andyw-lala/Tek7KTesters/Images/Aux_Y.png

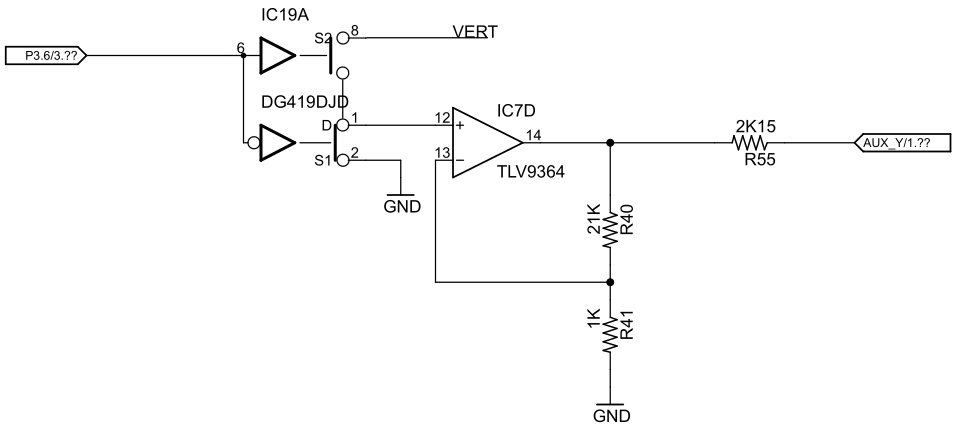
Images/Aux_Y.png
