andyw-lala/Tek7KTesters/Images/Aux_Z_Generator_20250103.png

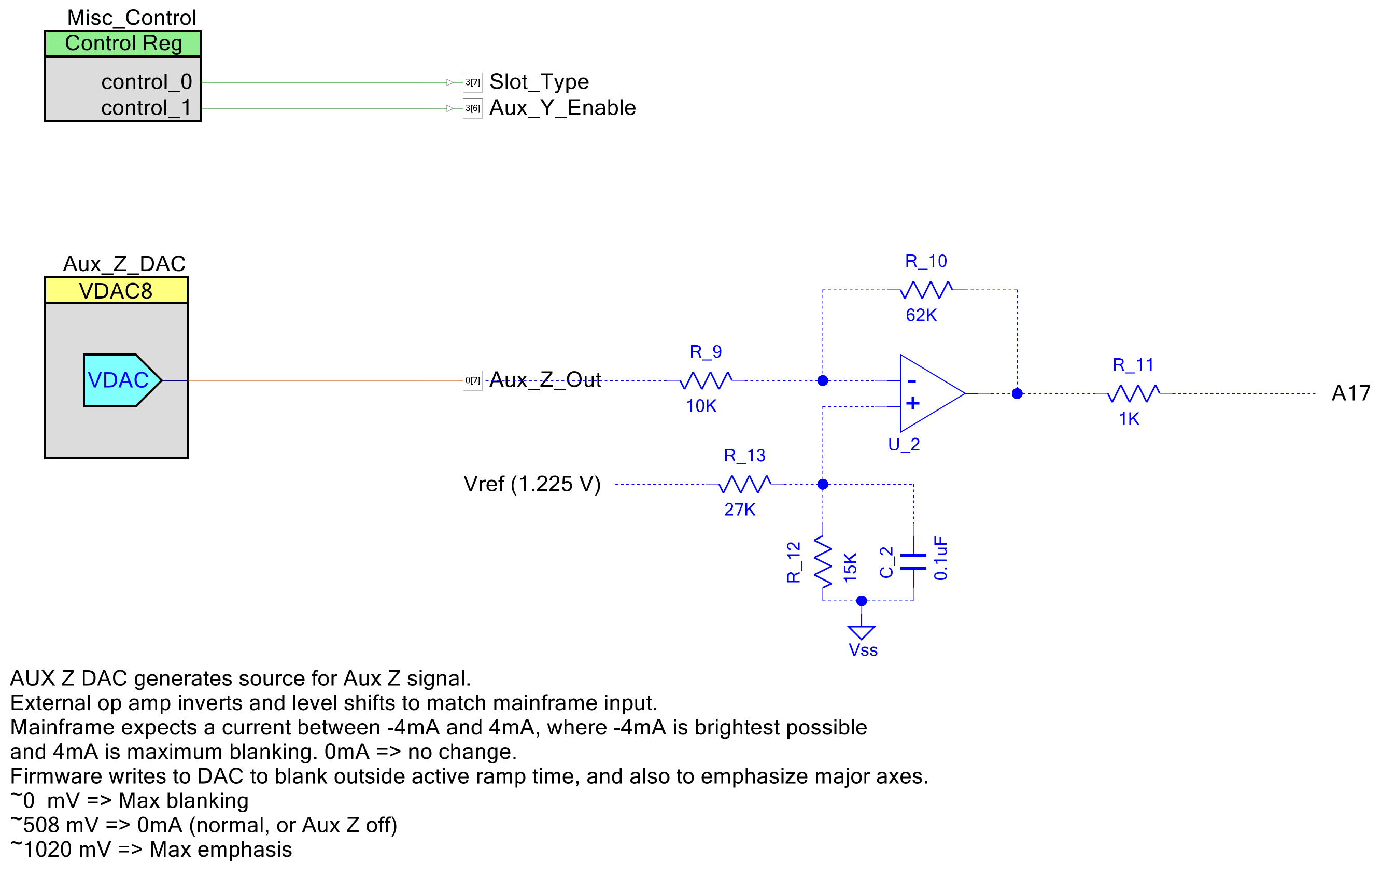
Images/Aux_Z_Generator_20250103.png
