andyw-lala/Tek7KTesters/Images/Discrete_timeslot_interface_snippet.png

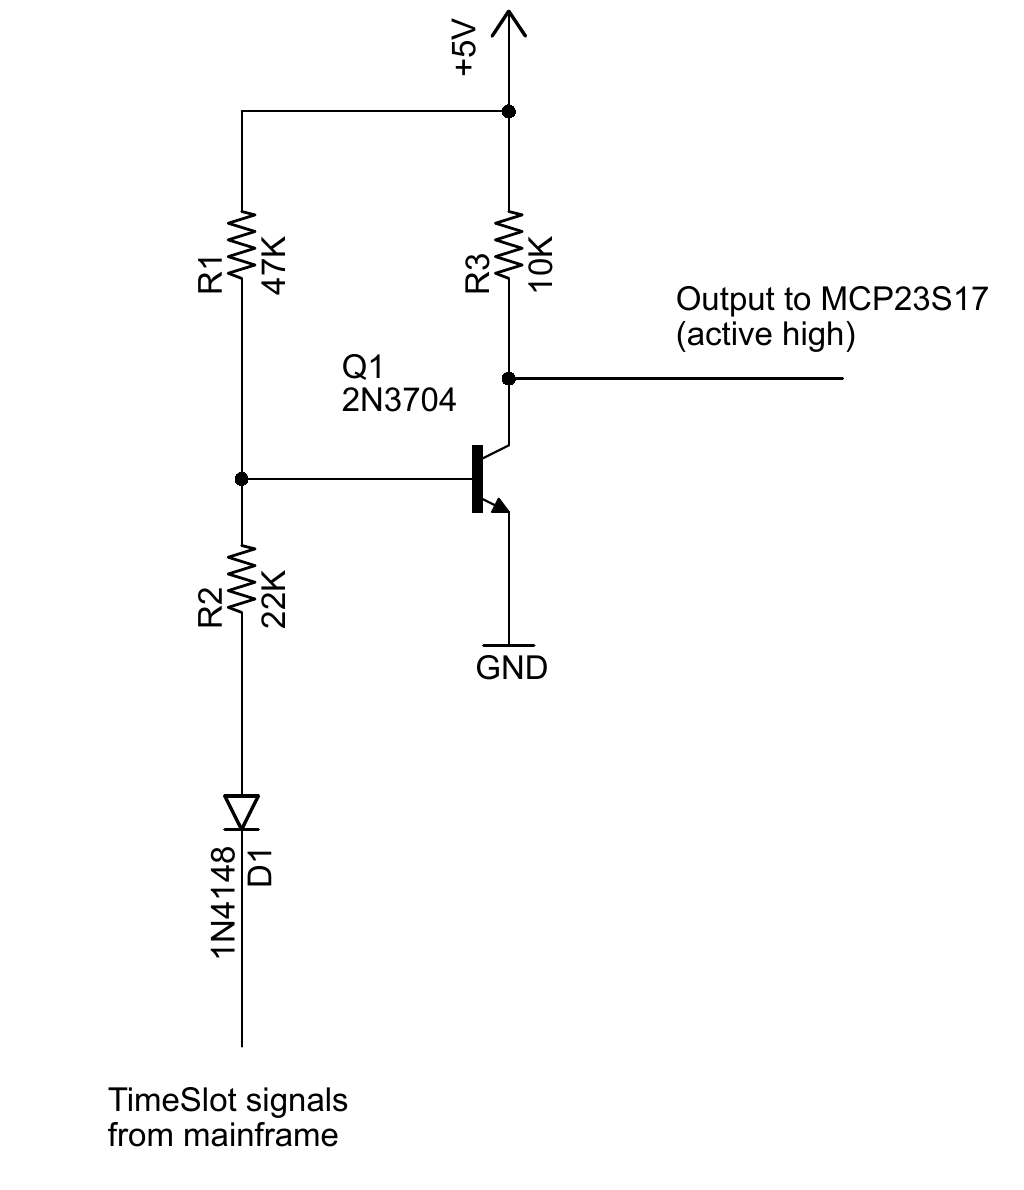
Images/Discrete_timeslot_interface_snippet.png
