andyw-lala/Tek7KTesters/Images/Ramp_Generator_20250103.png

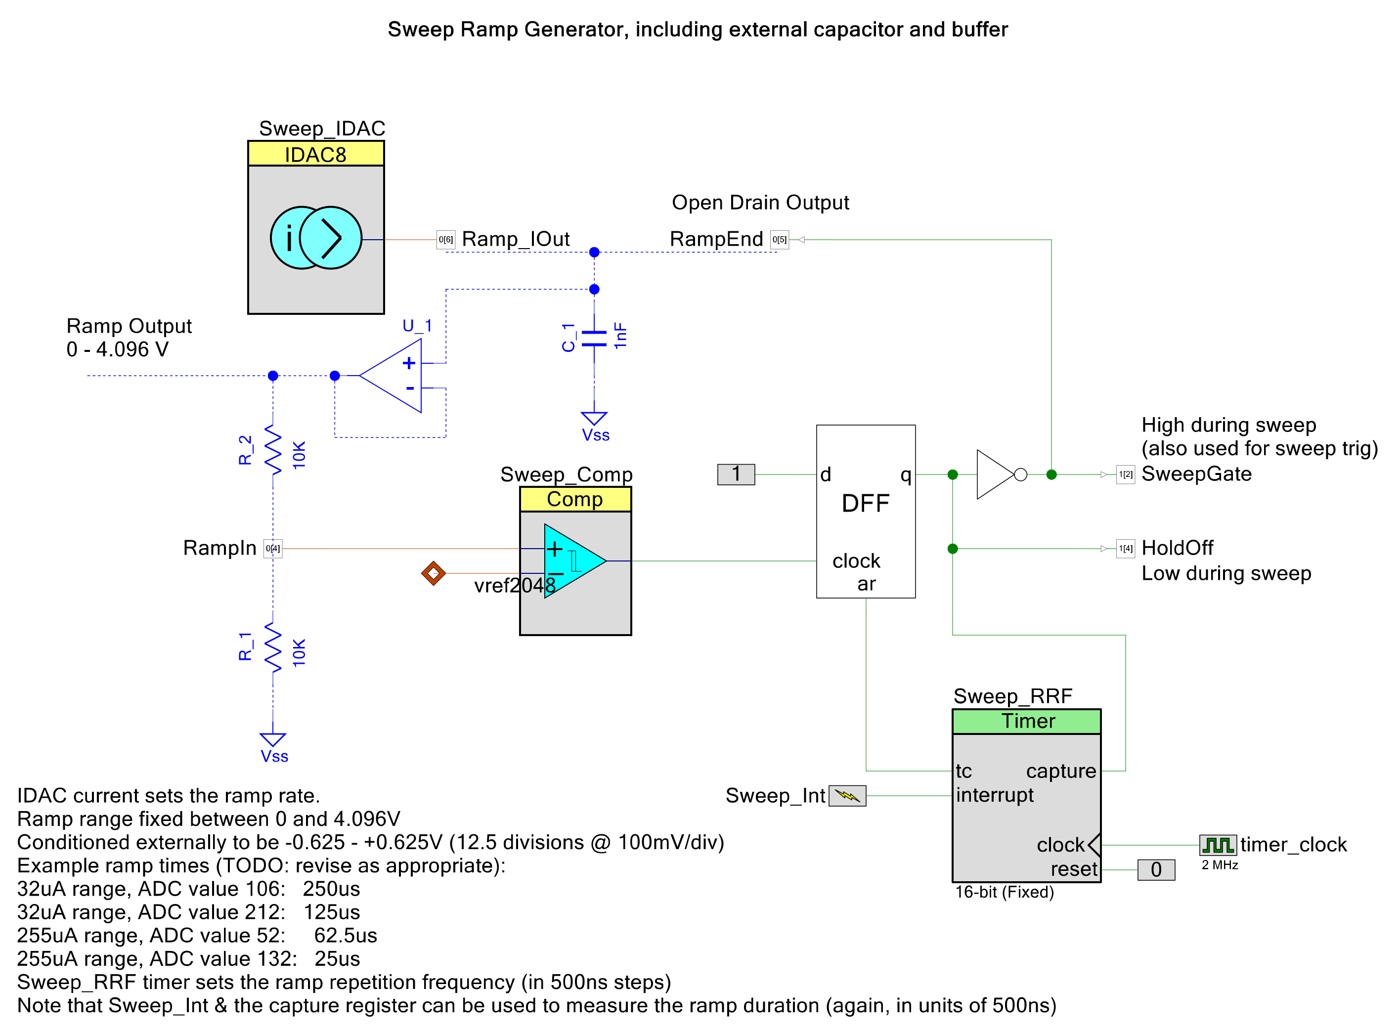
Images/Ramp_Generator_20250103.png
