andyw-lala/Tek7KTesters/Images/Readout_current_all.png

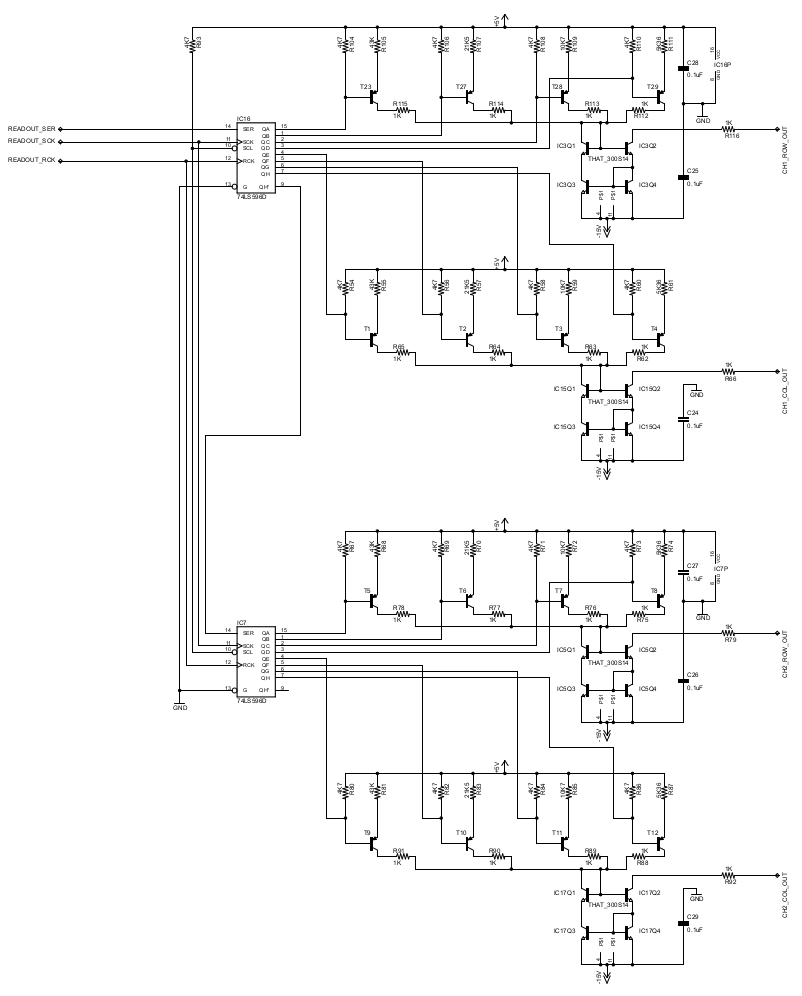
Images/Readout_current_all.png
