andyw-lala/Tek7KTesters/Images/Schmitt_trigger_timeslot_interface_snippet.png

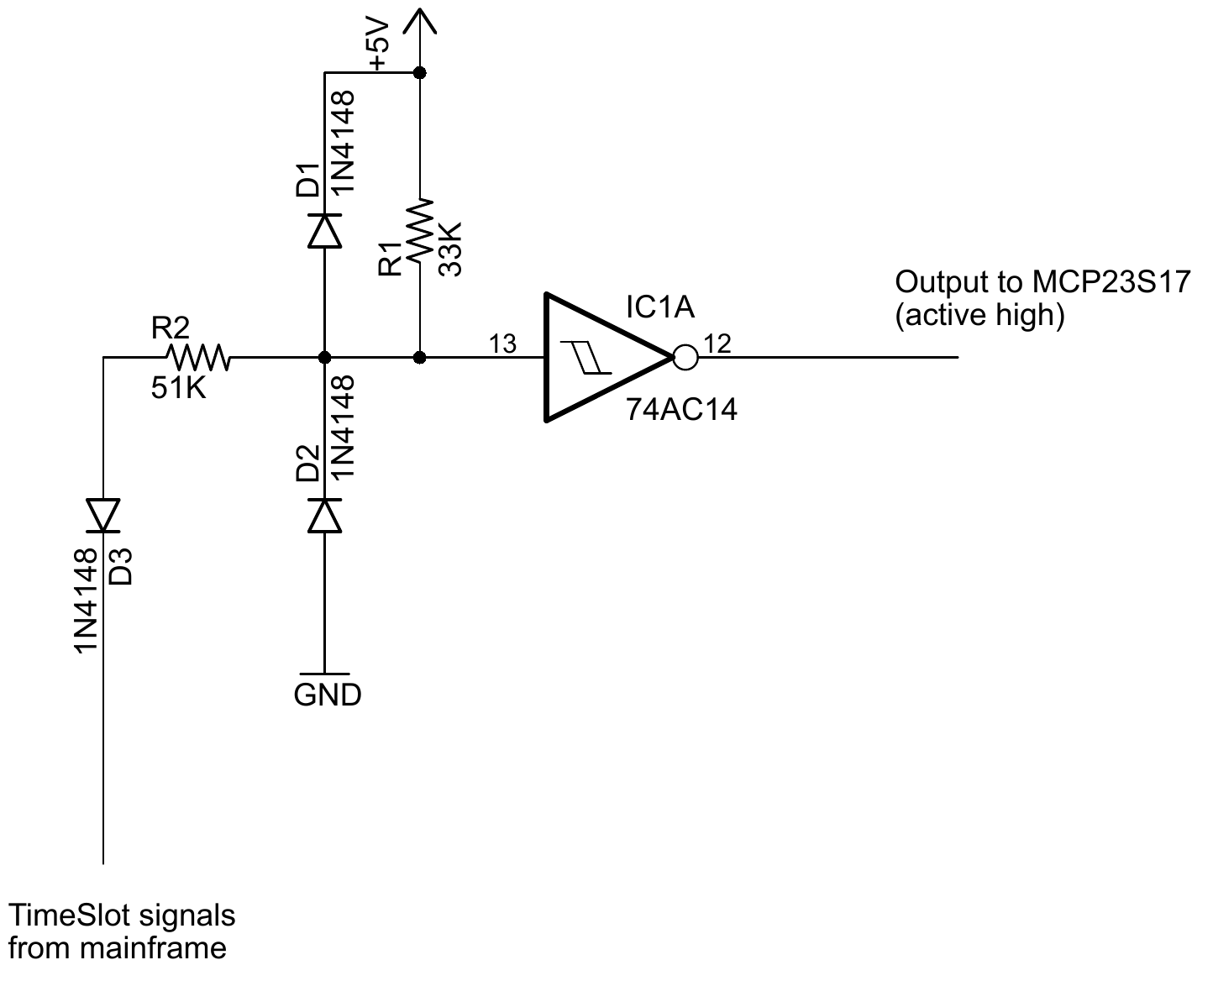
Images/Schmitt_trigger_timeslot_interface_snippet.png
