andyw-lala/Tek7KTesters/Images/Tek7K-TS0-202107271813.png

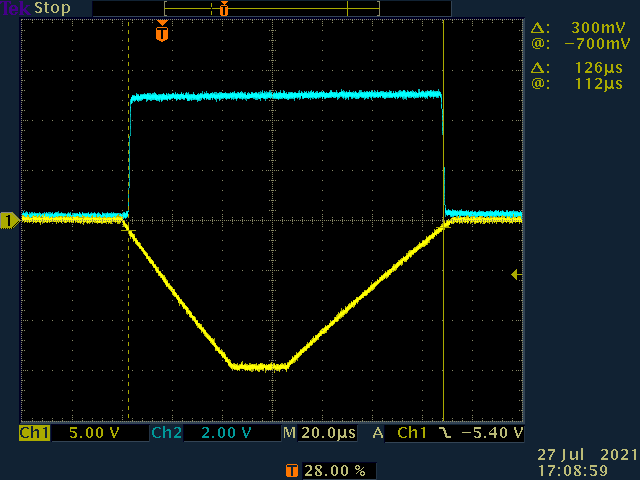
Images/Tek7K-TS0-202107271813.png
