andyw-lala/Tek7KTesters/Images/Tek7K-TS0-202107281441.png

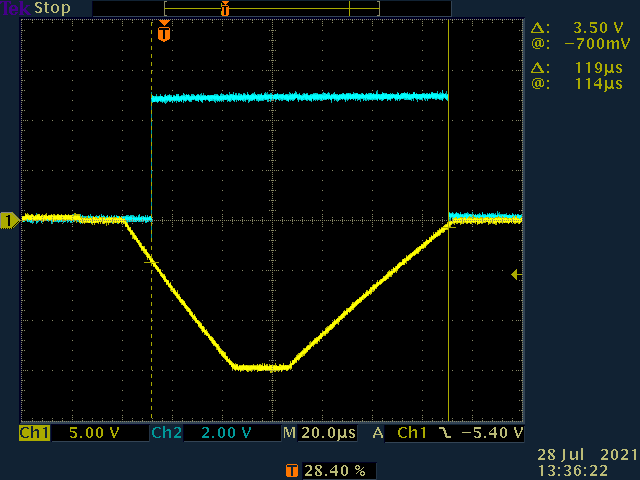
Images/Tek7K-TS0-202107281441.png
