andyw-lala/Tek7KTesters/Images/TS_Current_Sink.png

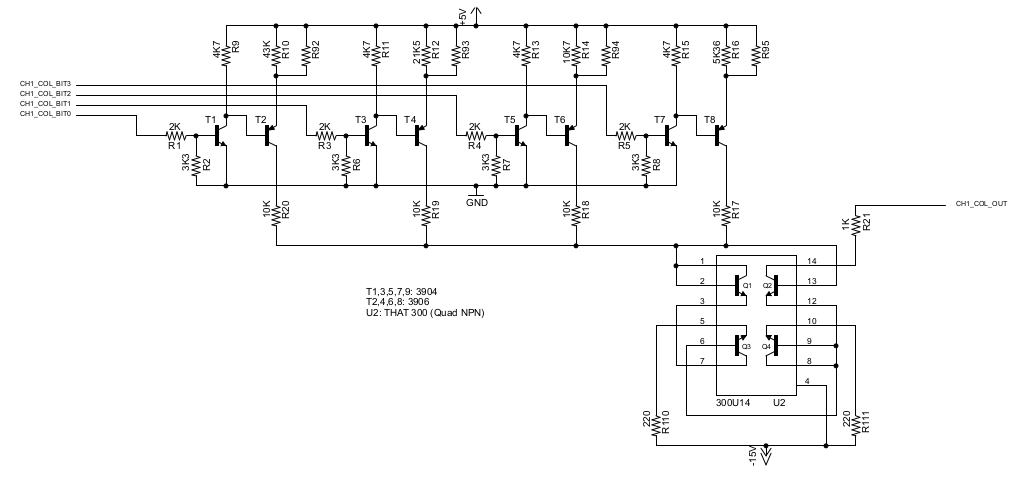
Images/TS_Current_Sink.png
