andyw-lala/Tek7KTesters/Images/TS_Current_Sink_2.png

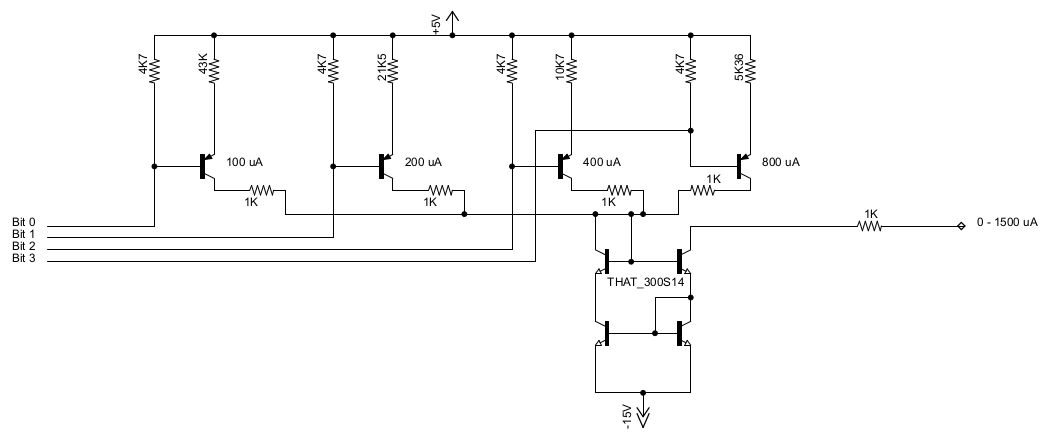
Images/TS_Current_Sink_2.png
