andyw-lala/Tek7KTesters/Images/TS_Output_Logic.png

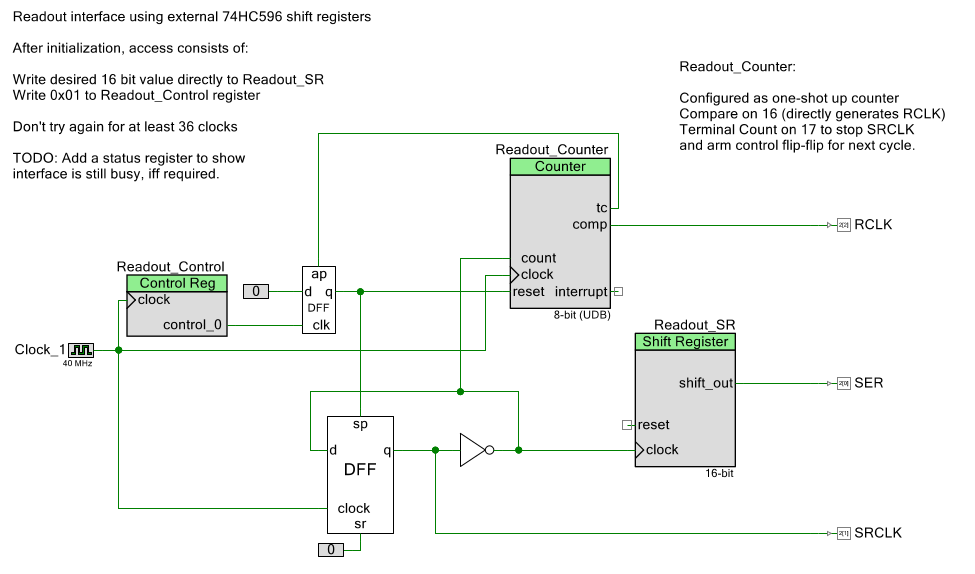
Images/TS_Output_Logic.png
