andyw-lala/Tek7KTesters/Images/TS_Pulse_Input_ISR_Timing.png

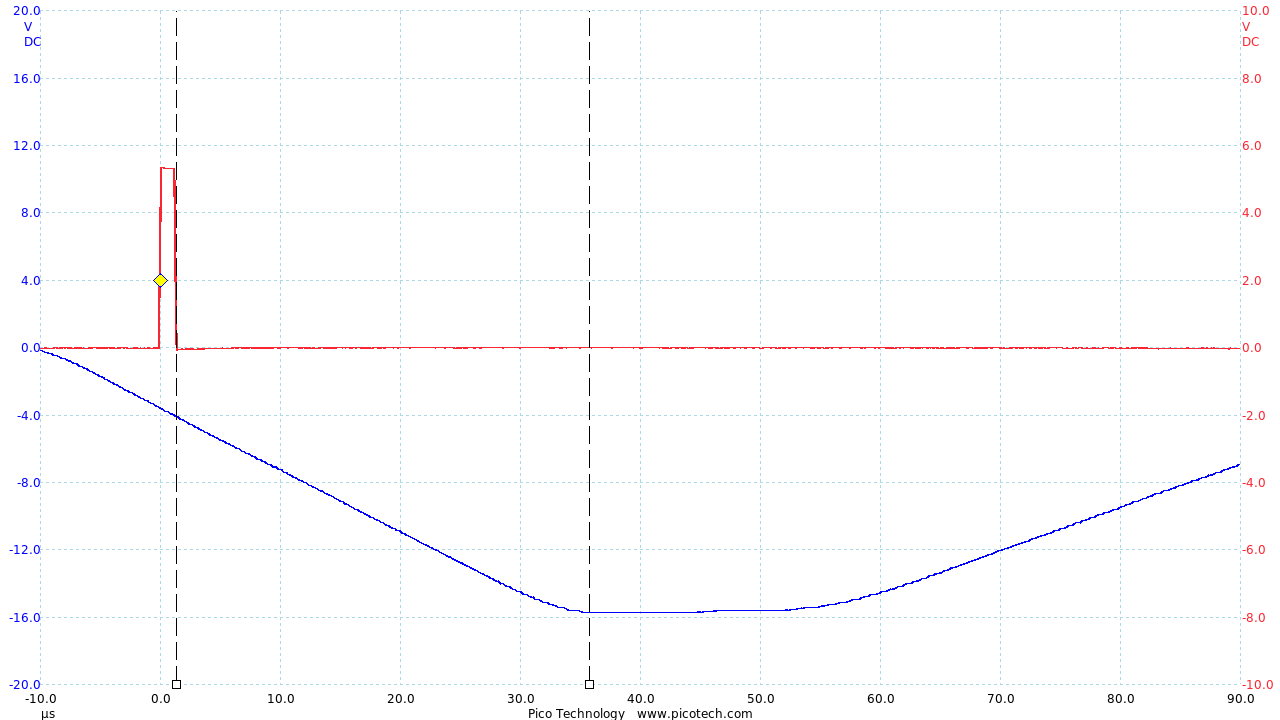
Images/TS_Pulse_Input_ISR_Timing.png
