andyw-lala/Tek7KTesters/Images/TS_Pulse_Inputs.png

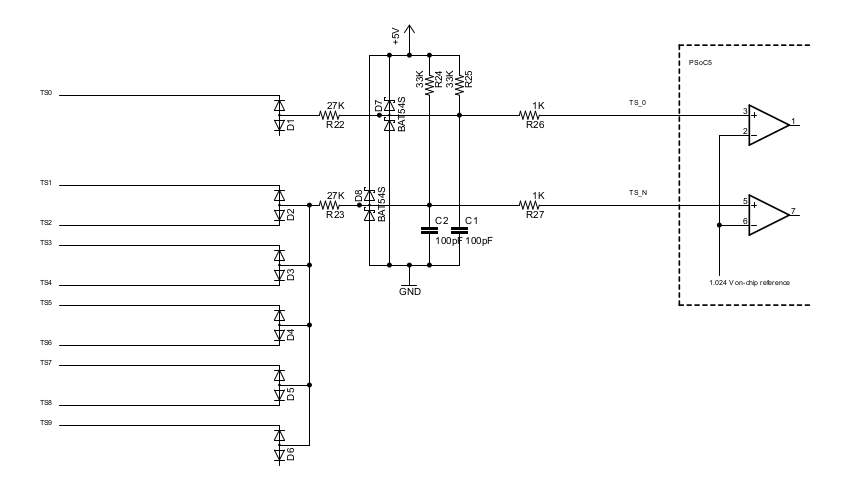
Images/TS_Pulse_Inputs.png
