andyw-lala/Tek7KTesters/Images/Step_Generators_20250103.png

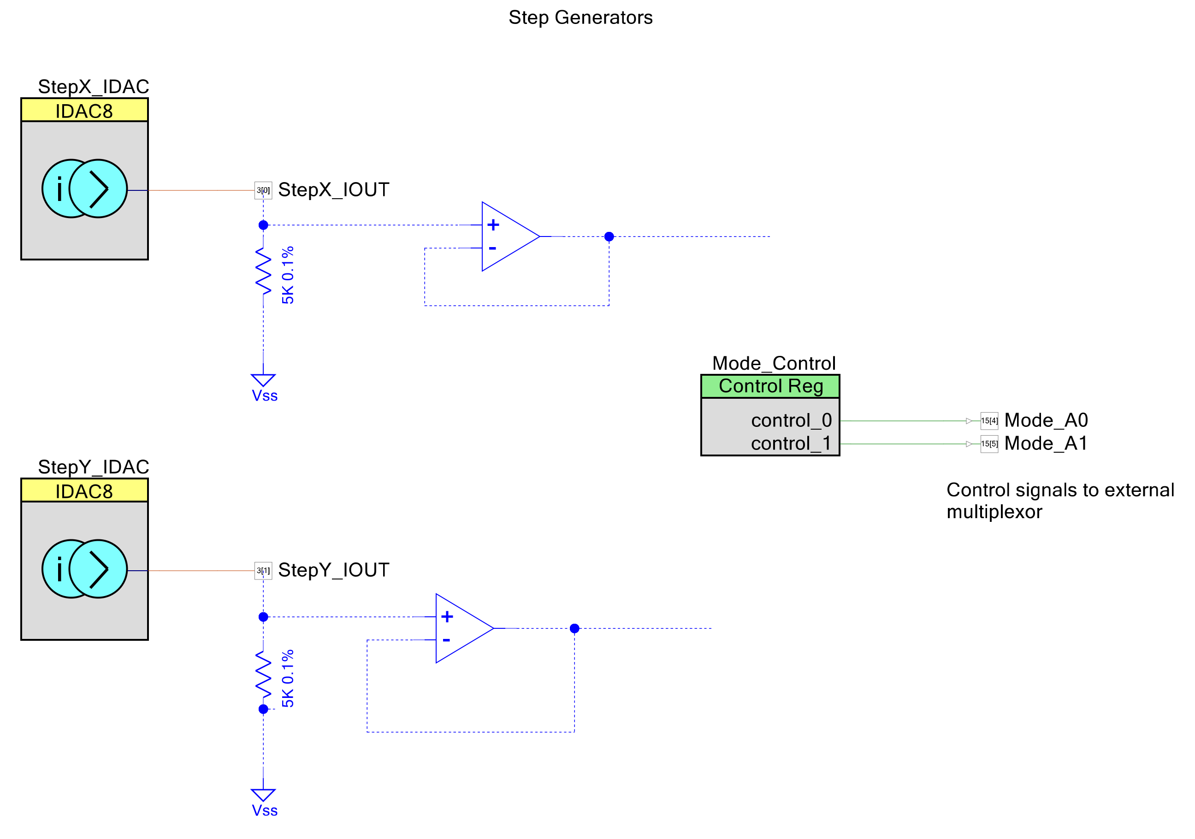
Images/Step_Generators_20250103.png
