andyw-lala/Tek7KTesters/Images/Steps.png

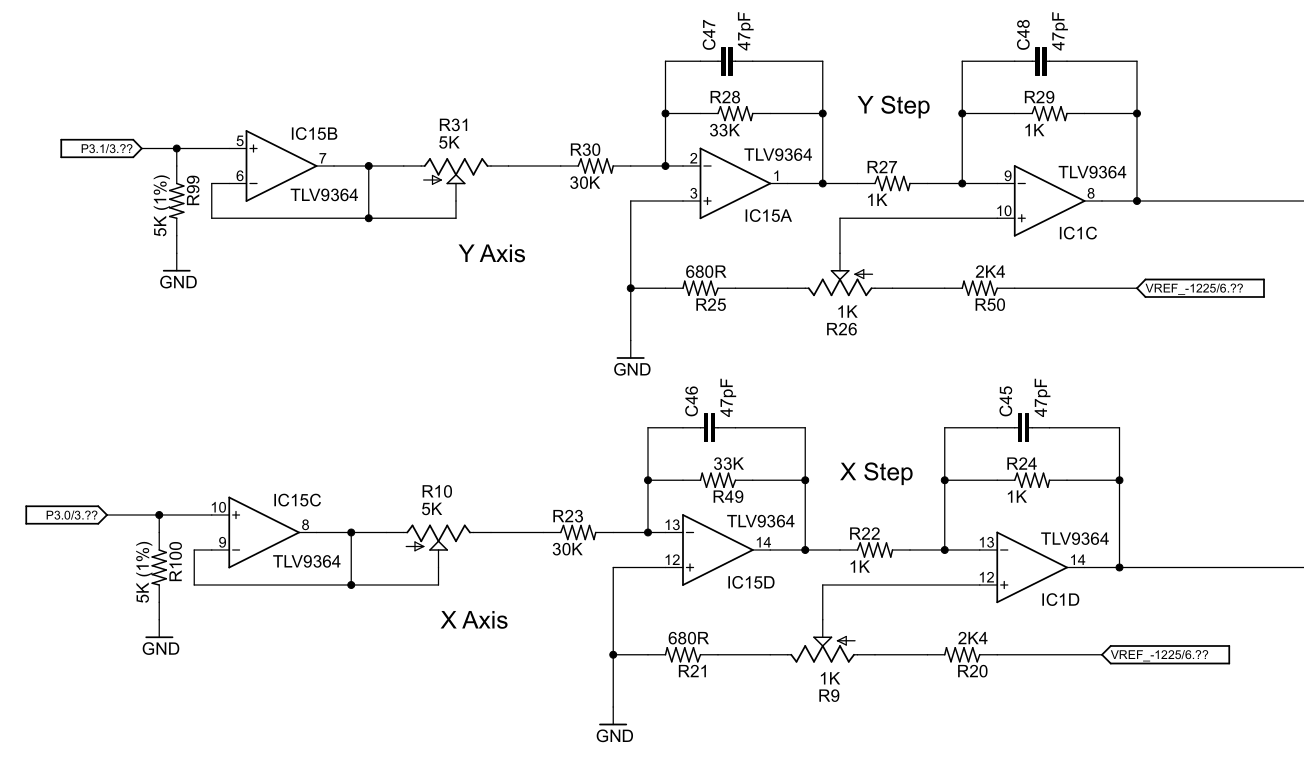
Images/Steps.png
