andyw-lala/Tek7KTesters/Tek7KTester_PSOC/Prototype_01.cydsn/lcd.c

#include "project.h"
#include "lcd.h"


	   
_lcd_dev lcddev;

uint16 POINT_COLOR = 0x0000,BACK_COLOR = 0xFFFF;  
uint16 DeviceCode;	 

/*****************************************************************************
 * @name       :void LCD_WR_REG(uint8 data)
 * @date       :2018-08-09 
 * @function   :Write an 8-bit command to the LCD screen
 * @parameters :data:Command value to be written
 * @retvalue   :None
******************************************************************************/
void LCD_WR_REG(uint8 data)
{ 
    LCD_CS_CLR;     
    LCD_RS_CLR;	  
    Display_SPI_WriteByte(data);
    LCD_CS_SET;	
}

/*****************************************************************************
 * @name       :void LCD_WR_DATA(uint8 data)
 * @date       :2018-08-09 
 * @function   :Write an 8-bit data to the LCD screen
 * @parameters :data:data value to be written
 * @retvalue   :None
******************************************************************************/
void LCD_WR_DATA(uint8 data)
{
    LCD_CS_CLR;
    LCD_RS_SET;
    Display_SPI_WriteByte(data);
    LCD_CS_SET;
}

/*****************************************************************************
 * @name       :void LCD_WriteReg(uint8 LCD_Reg, uint16 LCD_RegValue)
 * @date       :2018-08-09 
 * @function   :Write data into registers
 * @parameters :LCD_Reg:Register address
                LCD_RegValue:Data to be written
 * @retvalue   :None
******************************************************************************/
void LCD_WriteReg(uint8 LCD_Reg, uint16 LCD_RegValue)
{	
    LCD_WR_REG(LCD_Reg);  
    LCD_WR_DATA(LCD_RegValue);	    		 
}	   

/*****************************************************************************
 * @name       :void LCD_WriteRAM_Prepare(void)
 * @date       :2018-08-09 
 * @function   :Write GRAM
 * @parameters :None
 * @retvalue   :None
******************************************************************************/	 
void LCD_WriteRAM_Prepare(void)
{
    LCD_WR_REG(lcddev.wramcmd);
}	 

/*****************************************************************************
 * @name       :void Lcd_WriteData_16Bit(uint16 Data)
 * @date       :2018-08-09 
 * @function   :Write an 16-bit command to the LCD screen
 * @parameters :Data:Data to be written
 * @retvalue   :None
******************************************************************************/	 
void Lcd_WriteData_16Bit(uint16 Data)
{	
    LCD_CS_CLR;
    LCD_RS_SET;  
    Display_SPI_WriteByte(Data>>8);
    Display_SPI_WriteByte(Data);
    LCD_CS_SET;
}

/*****************************************************************************
 * @name       :void LCD_DrawPoint(uint16 x,uint16 y)
 * @date       :2018-08-09 
 * @function   :Write a pixel data at a specified location
 * @parameters :x:the x coordinate of the pixel
                y:the y coordinate of the pixel
 * @retvalue   :None
******************************************************************************/	
void LCD_DrawPoint(uint16 x,uint16 y)
{
    LCD_SetCursor(x,y);
    Lcd_WriteData_16Bit(POINT_COLOR); 
}

/*****************************************************************************
 * @name       :void LCD_Clear(uint16 Color)
 * @date       :2018-08-09 
 * @function   :Full screen filled LCD screen
 * @parameters :color:Filled color
 * @retvalue   :None
******************************************************************************/	
void LCD_Clear(uint16 Color)
{
    unsigned int i,m;  
    LCD_SetWindows(0,0,lcddev.width-1,lcddev.height-1);   
    LCD_CS_CLR;
    LCD_RS_SET;
    for(i=0;i<lcddev.height;i++) {
        for(m=0;m<lcddev.width;m++) {	
            Lcd_WriteData_16Bit(Color);
        }
    }
    LCD_CS_SET;
} 

/*****************************************************************************
 * @name       :void LCD_RESET(void)
 * @date       :2018-08-09 
 * @function   :Reset LCD screen
 * @parameters :None
 * @retvalue   :None
******************************************************************************/	
void LCD_RESET(void)
{
    LCD_RST_CLR;
    CyDelay(100);	
    LCD_RST_SET;
    CyDelay(50);
}

/*****************************************************************************
 * @name       :void LCD_RESET(void)
 * @date       :2018-08-09 
 * @function   :Initialization LCD screen
 * @parameters :None
 * @retvalue   :None
******************************************************************************/	 	 
void LCD_Init(void)
{  
    Display_SPI_Start();
    
    LCD_RESET();
    
    LCD_WR_REG(0xCF);  
    LCD_WR_DATA(0x00); 
    LCD_WR_DATA(0xD9); //0xC1 
    LCD_WR_DATA(0X30); 
    LCD_WR_REG(0xED);  
    LCD_WR_DATA(0x64); 
    LCD_WR_DATA(0x03); 
    LCD_WR_DATA(0X12); 
    LCD_WR_DATA(0X81); 
    LCD_WR_REG(0xE8);  
    LCD_WR_DATA(0x85); 
    LCD_WR_DATA(0x10); 
    LCD_WR_DATA(0x7A); 
    LCD_WR_REG(0xCB);  
    LCD_WR_DATA(0x39); 
    LCD_WR_DATA(0x2C); 
    LCD_WR_DATA(0x00); 
    LCD_WR_DATA(0x34); 
    LCD_WR_DATA(0x02); 
    LCD_WR_REG(0xF7);  
    LCD_WR_DATA(0x20); 
    LCD_WR_REG(0xEA);  
    LCD_WR_DATA(0x00); 
    LCD_WR_DATA(0x00); 
    LCD_WR_REG(0xC0);    //Power control 
    LCD_WR_DATA(0x1B);   //VRH[5:0] 
    LCD_WR_REG(0xC1);    //Power control 
    LCD_WR_DATA(0x12);   //SAP[2:0];BT[3:0] 0x01
    LCD_WR_REG(0xC5);    //VCM control 
    LCD_WR_DATA(0x08); 	 //30
    LCD_WR_DATA(0x26); 	 //30
    LCD_WR_REG(0xC7);    //VCM control2 
    LCD_WR_DATA(0XB7); 
    LCD_WR_REG(0x36);    // Memory Access Control 
    LCD_WR_DATA(0x08); 
    LCD_WR_REG(0x3A);   
    LCD_WR_DATA(0x55); 
    LCD_WR_REG(0xB1);   
    LCD_WR_DATA(0x00);   
    LCD_WR_DATA(0x1A); 
    LCD_WR_REG(0xB6);    // Display Function Control 
    LCD_WR_DATA(0x0A); 
    LCD_WR_DATA(0xA2); 
    LCD_WR_REG(0xF2);    // 3Gamma Function Disable 
    LCD_WR_DATA(0x00); 
    LCD_WR_REG(0x26);    //Gamma curve selected 
    LCD_WR_DATA(0x01); 
    LCD_WR_REG(0xE0);    //Set Gamma 
    LCD_WR_DATA(0x0F); 
    LCD_WR_DATA(0x1D); 
    LCD_WR_DATA(0x1A); 
    LCD_WR_DATA(0x0A); 
    LCD_WR_DATA(0x0D); 
    LCD_WR_DATA(0x07); 
    LCD_WR_DATA(0x49); 
    LCD_WR_DATA(0X66); 
    LCD_WR_DATA(0x3B); 
    LCD_WR_DATA(0x07); 
    LCD_WR_DATA(0x11); 
    LCD_WR_DATA(0x01); 
    LCD_WR_DATA(0x09); 
    LCD_WR_DATA(0x05); 
    LCD_WR_DATA(0x04); 		 
    LCD_WR_REG(0XE1);    //Set Gamma 
    LCD_WR_DATA(0x00); 
    LCD_WR_DATA(0x18); 
    LCD_WR_DATA(0x1D); 
    LCD_WR_DATA(0x02); 
    LCD_WR_DATA(0x0F); 
    LCD_WR_DATA(0x04); 
    LCD_WR_DATA(0x36); 
    LCD_WR_DATA(0x13); 
    LCD_WR_DATA(0x4C); 
    LCD_WR_DATA(0x07); 
    LCD_WR_DATA(0x13); 
    LCD_WR_DATA(0x0F); 
    LCD_WR_DATA(0x2E); 
    LCD_WR_DATA(0x2F); 
    LCD_WR_DATA(0x05); 
    LCD_WR_REG(0x2B); 
    LCD_WR_DATA(0x00);
    LCD_WR_DATA(0x00);
    LCD_WR_DATA(0x01);
    LCD_WR_DATA(0x3f);
    LCD_WR_REG(0x2A); 
    LCD_WR_DATA(0x00);
    LCD_WR_DATA(0x00);
    LCD_WR_DATA(0x00);
    LCD_WR_DATA(0xef);	 
    LCD_WR_REG(0x11); //Exit Sleep
    CyDelay(120);
    LCD_WR_REG(0x29); //display on		
    
    LCD_direction(USE_HORIZONTAL);
    
    LCD_Clear(CYAN);
}
 
/*****************************************************************************
 * @name       :void LCD_SetWindows(uint16 xStar, uint16 yStar,uint16 xEnd,uint16 yEnd)
 * @date       :2018-08-09 
 * @function   :Setting LCD display window
 * @parameters :xStart:the beginning x coordinate of the LCD display window
		yStart:the beginning y coordinate of the LCD display window
		xEnd:the ending x coordinate of the LCD display window
		yEnd:the ending y coordinate of the LCD display window
 * @retvalue   :None
******************************************************************************/ 
void LCD_SetWindows(uint16 xStart, uint16 yStart,uint16 xEnd,uint16 yEnd)
{	
    LCD_WR_REG(lcddev.setxcmd);	
    LCD_WR_DATA(xStart>>8);
    LCD_WR_DATA(0x00FF&xStart);		
    LCD_WR_DATA(xEnd>>8);
    LCD_WR_DATA(0x00FF&xEnd);

    LCD_WR_REG(lcddev.setycmd);	
    LCD_WR_DATA(yStart>>8);
    LCD_WR_DATA(0x00FF&yStart);		
    LCD_WR_DATA(yEnd>>8);
    LCD_WR_DATA(0x00FF&yEnd);

    LCD_WriteRAM_Prepare();
}   

/*****************************************************************************
 * @name       :void LCD_SetCursor(uint16 Xpos, uint16 Ypos)
 * @date       :2018-08-09 
 * @function   :Set coordinate value
 * @parameters :Xpos:the  x coordinate of the pixel
		Ypos:the  y coordinate of the pixel
 * @retvalue   :None
******************************************************************************/ 
void LCD_SetCursor(uint16 Xpos, uint16 Ypos)
{	  	    			
    LCD_SetWindows(Xpos,Ypos,Xpos,Ypos);	
} 

/*****************************************************************************
 * @name       :void LCD_direction(uint8 direction)
 * @date       :2018-08-09 
 * @function   :Setting the display direction of LCD screen
 * @parameters :direction:0-0 degree
		  	1-90 degree
			2-180 degree
			3-270 degree
 * @retvalue   :None
******************************************************************************/ 
void LCD_direction(uint8 direction)
{ 
    lcddev.setxcmd=0x2A;
    lcddev.setycmd=0x2B;
    lcddev.wramcmd=0x2C;
    switch(direction){		  
        case 0:						 	 		
            lcddev.width=LCD_W;
            lcddev.height=LCD_H;		
            LCD_WriteReg(0x36,(1<<3)|(0<<6)|(0<<7));//BGR==1,MY==0,MX==0,MV==0
            break;
        case 1:
            lcddev.width=LCD_H;
            lcddev.height=LCD_W;
            LCD_WriteReg(0x36,(1<<3)|(0<<7)|(1<<6)|(1<<5));//BGR==1,MY==1,MX==0,MV==1
            break;
        case 2:						 	 		
            lcddev.width=LCD_W;
            lcddev.height=LCD_H;	
            LCD_WriteReg(0x36,(1<<3)|(1<<6)|(1<<7));//BGR==1,MY==0,MX==0,MV==0
            break;
        case 3:
            lcddev.width=LCD_H;
            lcddev.height=LCD_W;
            LCD_WriteReg(0x36,(1<<3)|(1<<7)|(1<<5));//BGR==1,MY==1,MX==0,MV==1
            break;	
        default:
            break;
    }		
}	 
